schimen/killer-robot/command_lib/zephyr/command.c

#include "command.h"

// Register logger for command-lib
LOG_MODULE_REGISTER(command);

// Create incoming command queue and ack event for acks
K_MSGQ_DEFINE(incoming_commands, sizeof(struct command_data), MAX_MSGS, 4);
K_EVENT_DEFINE(ack_event);

uint8_t get_message_id() {
    static uint8_t message_id = 0;
    if (message_id >= 32) {
        message_id = 0;
    } else {
        message_id++;
    }
    return message_id;
}

void set_ack(uint8_t id) { k_event_set(&ack_event, (1 << id)); }

int wait_for_ack(uint8_t id, int64_t *receive_time) {
    int64_t start_time = k_uptime_get();
    if (k_event_wait(&ack_event, (1 << id), true, ACK_TIMEOUT) == 0) {
        return 1;
    }
    // Compute passed time in milliseconds
    *receive_time = k_uptime_delta(&start_time);
    if (*receive_time > 255) {
        // time is out of bounds for 8 bit value in command
        *receive_time = 255;
    }
    return 0;
}

void add_command(struct command_data command) {
    // Add new command to incoming commands
    while (k_msgq_put(&incoming_commands, &command, K_NO_WAIT) != 0) {
        // message queue is full, purge and try again
        LOG_WRN("Message queue full, purging message-queue");
        k_msgq_purge(&incoming_commands);
    }
}

int get_command(struct command_data *command) {
    return k_msgq_get(&incoming_commands, command, COMMAND_TIMEOUT);
}

int send_command(struct command_data command) {
    // Make sure command writer and send-function exists
    if (command.writer == NULL) {
        LOG_ERR("Failed to send, no command writer");
        return -1;
    }
    if (command.writer->send_command_func == NULL) {
        LOG_ERR("Failed to send, no send function");
        return -1;
    }
    // Send command and return result
    return (command.writer->send_command_func)(command);
}

void send_ack(struct command_data command, uint8_t receive_time) {
    command.key = ack_command;
    command.value = receive_time;
    send_command(command);
}

void send_error(struct command_data command, uint8_t error_code) {
    command.key = error_command;
    command.value = error_code;
    send_command(command);
}

uint8_t send_ping(struct command_writer *writer) {
    struct command_data command;
    command.key = ping_command;
    command.id = get_message_id();
    command.value = 0;
    if (send_command(command)) {
        LOG_ERR("Failed to send ping (id: %d)", command.id);
    }
    return command.id;
}
